PDanner-EI/ergoboard/obsidian/Keyboards/_images/kb_cosmos_model.png

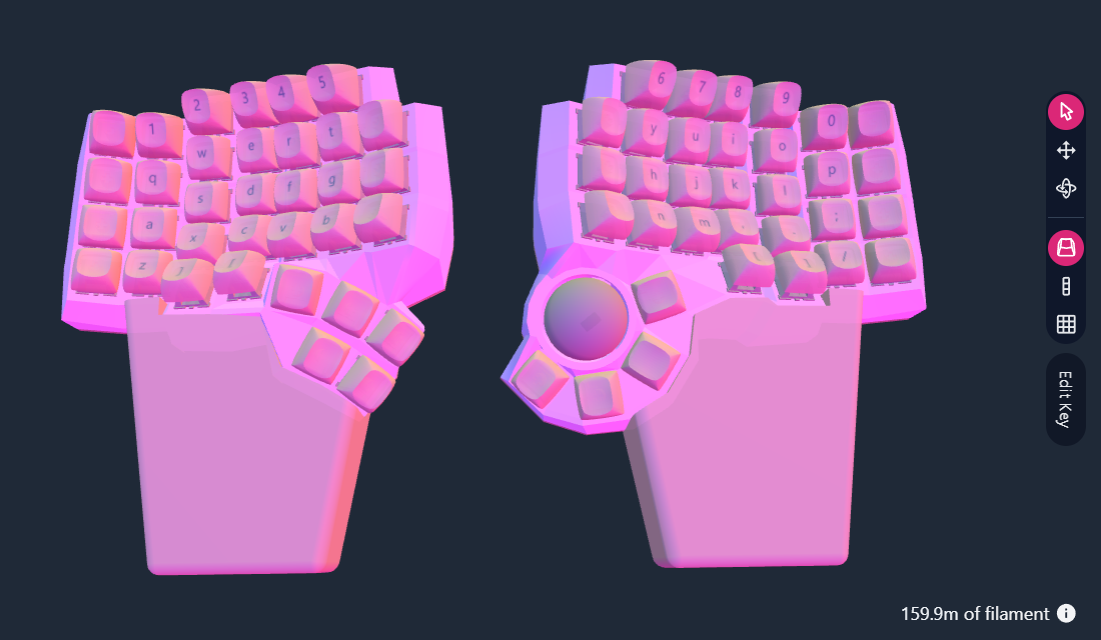
obsidian/Keyboards/_images/kb_cosmos_model.png
