PDanner-EI/ergoboard/obsidian/Keyboards/_images/kb_cosmos_model_V1.png

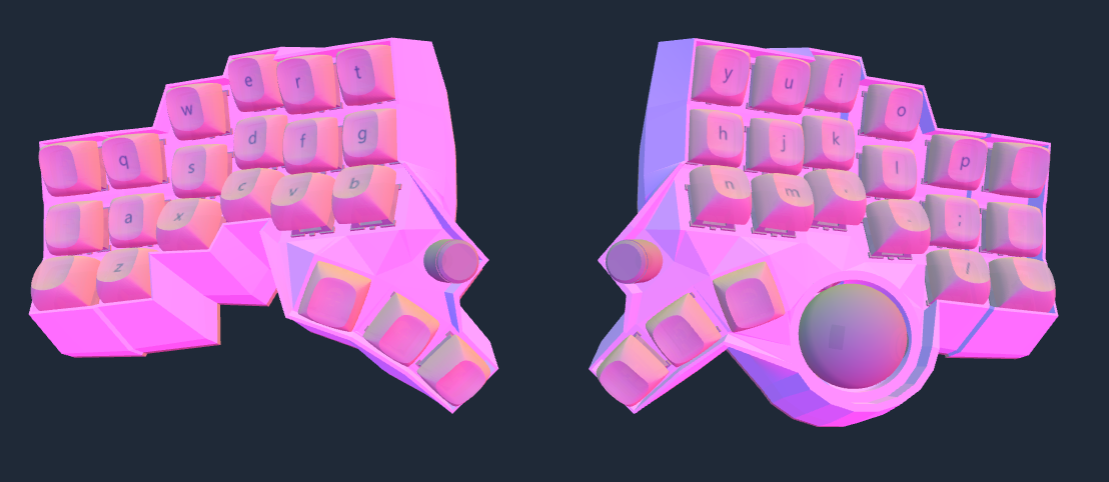
obsidian/Keyboards/_images/kb_cosmos_model_V1.png
