PDanner-EI/ergoboard/obsidian/Keyboards/_images/kb_kinesis_advantage_360.png

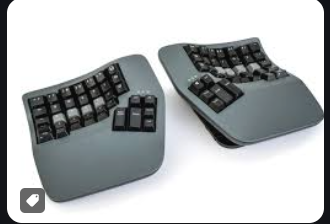
obsidian/Keyboards/_images/kb_kinesis_advantage_360.png
