PDanner-EI/ergoboard/obsidian/Keyboards/_images/kb_microsoft_sculpt_ergonomic.png

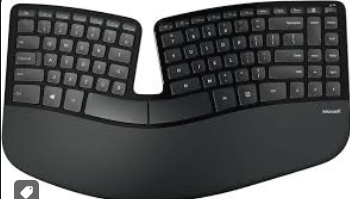
obsidian/Keyboards/_images/kb_microsoft_sculpt_ergonomic.png
